wum747349-debug/STM32-24V-Industrial-IO-Bridge/references/README.md

# Local References（本地资料）

这里只保存与当前 Project 相关的本地 Evidence，并在真实内容存在时创建子目录。常见 Conditional content 包括按模块整理的 datasheet、supplier-search notes、standards 与 mechanical documents。

官方 datasheet、reference manual 与 application note 是关键参数的主要来源。Supplier page 只辅助采购，不能替代官方技术证据；每项来源及用途记录在根 `references.md`。
